MustafaTpbs/Newcom-Polytech/rh_com_piste/antennes.py

from enum import Enum

class Way(Enum):
   EW = 0
   NS = 3

class Antennes_EW(Enum):
   EXT0  = 0  
   EXT1  = 1  
   EXT2  = 2  
   EW1   = 3  
   EW2   = 4  
   EW3   = 5  
   EW4   = 6  
   EW5   = 7  
   EW6   = 8  
   EW7   = 9  
   EW8   = 10 
   EW9   = 11 
   EW10  = 12 
   EW11  = 13 
   EW12  = 14 
   EW13  = 15 
   EW14  = 16 
   EW15  = 17 
   EW16  = 18 
   AA0   = 19 
   AA1   = 20 
   AA2   = 21 
   AA3   = 22 

class Antennes_NS(Enum):
   NS0  = 0  
   NS1  = 1  
   NS2  = 2  
   NS3  = 3  
   NS4  = 4  
   NS5  = 5  
   NS6  = 6  
   NS7  = 7  
   NS8  = 8  
   NS9  = 9  
   NS10 = 10 
   NS11 = 11 
   NS12 = 12 
   NS13 = 13 
   NS14 = 14 
   NS15 = 15 
   NS16 = 16 
   NS17 = 17 
   NS18 = 18 
   NS19 = 19 
   NS20 = 20 
   NS21 = 21 
   NS22 = 22 
   NS23 = 23 
   NS24 = 24 
