MustafaTpbs/Newcom-Polytech/rh_com_piste/frequence.py

FREQUENCE = [None] * 10

#FREQUENCE[0] = 228  
#FREQUENCE[1] = 298.7
##FREQUENCE[2] = 360.8
#FREQUENCE[2] = 666
##FREQUENCE[3] = 327  
#FREQUENCE[3] = 666
#FREQUENCE[4] = 270.6
#FREQUENCE[5] = 445  
#FREQUENCE[6] = 408  
#FREQUENCE[7] = 150.9
#FREQUENCE[8] = 173.2
#FREQUENCE[9] = 432.9

FREQUENCE[0] = 228  
FREQUENCE[1] = 298.7
#FREQUENCE[2] = 666
FREQUENCE[2] = 382.2
FREQUENCE[3] = 370
FREQUENCE[4] = 270.6
FREQUENCE[5] = 444  
FREQUENCE[6] = 408  
FREQUENCE[7] = 150.9
FREQUENCE[8] = 173.2
FREQUENCE[9] = 432.9

#FREQUENCE[0] = 150.9  
#FREQUENCE[1] = 270.6
##FREQUENCE[2] = 666
#FREQUENCE[2] = 298.7
#FREQUENCE[3] = 360.8
#FREQUENCE[4] = 445
#FREQUENCE[5] = 150.9  
#FREQUENCE[6] = 280  
#FREQUENCE[7] = 150.9
#FREQUENCE[8] = 173.2
#FREQUENCE[9] = 432.9
