MustafaTpbs/Newcom-Polytech/rh_com_piste/walsh.py

from enum import Enum

class FunctionsWalsh(Enum):
  #WALSH_JEUX_0        = 0x38
  #KIKI5               = 0X0539
  #WALSH_JEUX_1        = 0x39
  #WALSH_JEUX_2        = 0x3A
  #WALSH_JEUX_3        = 0x3B
  #WALSH_OFF           = 0x3C
  #WALSH_OFF_H_BLOCKED = 0x3D
  #WALSH_OFF_V_BLOCKED = 0x3E
  INERTE_CMD          = 0x28
  MODE_0               = 0X0039
  MODE_4               = 0X0439
  MODE_7               = 0X0739
  MODE_6               = 0X0639
  MODE_2               = 0X0239
  MODE_5               = 0X0539
  MODE_1               = 0X0139
  #KIKI8               = 0X0839
  #KIKIC               = 0X0C39
  #KIKIF               = 0X0F39
  #KIKIE               = 0X0E39
  #KIKIA               = 0X0A39
  #KIKID               = 0X0D39
  #KIKI9               = 0X0939#
